colwilliamsnz/YAORP32/Arduino/logos.h

// Wattle Labs Logo
static const unsigned char icon_logo[] U8X8_PROGMEM = {0x00,0x00,0x07,0x00,0x00,0x00,0x80,0x19,0x00,0x00,0x00,0x80,0x10,0x00,0x00,0x00,0xc0,0x10,0x00,0x00,0x00,0x80,0x10,0x00,0x00,0x00,0x80,0x19,0x00,0x00,0x00,0x00,0x0f,0x00,0x00,0x3e,0x00,0x06,0x00,0x00,0x62,0x00,0x06,0x00,0x00,0x61,0x00,0x06,0x00,0x00,0x41,0x00,0x06,0x00,0x00,0x63,0x00,0x06,0x00,0x00,0xfe,0x01,0x06,0x00,0x00,0x1c,0x07,0x06,0xc0,0x01,0x00,0x0e,0x06,0x20,0x03,0x00,0x38,0x06,0x30,0x06,0x00,0xe0,0x06,0x10,0x04,0x00,0xc0,0x07,0x30,0x06,0x00,0x00,0x07,0xfc,0x03,0x00,0x00,0x06,0xce,0x01,0x1c,0x00,0x86,0x03,0x00,0x3e,0x00,0xe6,0x00,0x00,0x63,0x00,0x3e,0x00,0x00,0x41,0x00,0x1e,0x00,0x00,0x63,0x00,0x06,0x00,0x00,0xf2,0x00,0x06,0x00,0x00,0xbc,0x03,0x06,0xc0,0x01,0x00,0x0e,0x06,0xe0,0x03,0x00,0x1c,0x06,0x30,0x06,0x00,0x70,0x06,0x10,0x04,0x00,0xc0,0x07,0x30,0x04,0x00,0x80,0x07,0x38,0x02,0x00,0x00,0x06,0xee,0x01,0x00,0x00,0x86,0x03,0x00,0x00,0x00,0xc6,0x01,0x00,0x7e,0x00,0x76,0x00,0x00,0xfe,0x01,0x1e,0x00,0x00,0xfc,0x07,0x0e,0x00,0x00,0xfc,0x0f,0x06,0x00,0x00,0xfc,0x1f,0x06,0x00,0x00,0xf8,0x3f,0x06,0x00,0x00,0xf8,0x7f,0x06,0x80,0x03,0xf0,0x7f,0x06,0xf8,0x03,0x30,0xfc,0x06,0xfe,0x03,0xe0,0xff,0x06,0xbf,0x01,0xc0,0xef,0x86,0xdf,0x01,0x80,0xff,0xc7,0xef,0x00,0x00,0xff,0xe7,0xf7,0x00,0x00,0xfe,0xf7,0xfb,0x00,0x00,0xf0,0xf7,0x7d,0x00,0x00,0x00,0xff,0x3e,0x00,0x00,0x00,0x7e,0x3f,0x00,0x00,0x00,0xbe,0x1f,0x00,0x00,0x00,0xfe,0x07,0x00,0x00,0x00,0xfe,0x03,0x00,0x00,0x00,0xfe,0x00,0x00,0x00,0x00,0x06,0x00,0x00,0x00,0x00,0x06,0x00,0x00,0x00,0x00,0x06,0x00,0x00,0x00,0x00,0x06,0x00,0x00,0x00,0x00,0x06,0x00,0x00,0x00,0x00,0x06,0x00,0x00,0x00,0x00,0x06,0x00,0x00,0x00,0x00,0x02,0x00,0x00};

// Thermometer Icon
static const unsigned char icon_temperature[] U8X8_PROGMEM = {0x38,0x00,0x44,0x40,0xd4,0xa0,0x54,0x40,0xd4,0x1c,0x54,0x06,0xd4,0x02,0x54,0x02,0x54,0x06,0x92,0x1c,0x39,0x01,0x75,0x01,0x7d,0x01,0x39,0x01,0x82,0x00,0x7c,0x00};
